supermoun62/Github_Projet_Train_Sons/Materiel_Projet_Trains_Sons/Materiels_Projet_Trains_Sons.pdf

Matériels_Projet_Train_Sons

# | Reference | Qty | Value | Footprint | TME-EU | TME-EU

1 | A1 | 1 | Arduino_Nano_v3.x | Module:Arduino_Nano
| Support mâle-femelle 15br | 2
2 | C1 | 1 | 330nf-25v | MesEmpreintes:CK06BX334K | CK06BX334K | ECQE2334KF
3 | C2 | 1 | 100nf-25v | MesEmpreintes:C_Disc_D5.0mm_W2.5mm_P2.50mm | CCK-100N
4 | C3 | 1 | 2200uf-35v | Capacitor_THT:CP_Radial_D17.0mm_P7.50mm | EEUFR1V222
5 | C4 | 1 | 47uf-16v | Capacitor_THT:CP_Radial_D5.0mm_P2.50mm | ECEA1CKS470
6 | D1 | 1 | B40C1500G | MesEmpreintes:B40C1500GE4851 | B40C1500G-E4/51
7 | D2 | 1 | 1N4007 | Diode_THT:D_DO-41_SOD81_P10.16mm_Horizontal | 1N4007-DC
8 | D3 | 1 | LED-5mm | LED_THT:LED_D5.0mm
9 | D4 | 1 | Busy | LED_THT:LED_D5.0mm
10 | D5 | 1 | Def SD | LED_THT:LED_D5.0mm
11 | D6 | 1 | E1 | LED_THT:LED_D5.0mm
12 | D7 | 1 | E2 | LED_THT:LED_D5.0mm
13 | F1 | 1 | | MesEmpreintes:Fuseholder_Cylinder-5x20mm_ Schurter_ZHL7X-H_Horizontal_Open | ZHL75
| F1 | 1 | | Support | ZHL7X-H
| Fusible | 1 | 250ma | | 0034.1510
14 | J1 | 1 | 1888690 | MesEmpreintes:MKDSN2,5-3-5,08-1888690 | MKDSN2.5/3-5.08
15 | J2, J3, J5, J8 | 4 | Conn_01x02_Socket | Connector_PinHeader_2.54mm:PinHeader_1x02_P2.54mm_Vertical
16 | J4 | 1 | Conn_01x05_Socket | Connector_PinHeader_2.54mm:PinHeader_1x05_P2.54mm_Vertical
17 | J6 | 1 | Conn_01x07_Socket | Connector_PinHeader_2.54mm:PinHeader_1x07_P2.54mm_Vertical
18 | J7 | 1 | Conn_01x03_Socket | Connector_PinHeader_2.54mm:PinHeader_1x03_P2.54mm_Vertical
19 | R1 | 1 | 1k-1 % | Resistor_THT:R_Axial_DIN0207_L6.3mm_D2.5mm_P2.54mm_Vertical | MBB02070C1001FCT00
20 | R2 | 1 | 4.7k-1% | Resistor_THT:R_Axial_DIN0207_L6.3mm_D2.5mm_P2.54mm_Vertical | MBA02040C4701FCT00
21 | R3, R8 | 2 | ? | Resistor_THT:R_Axial_DIN0207_L6.3mm_D2.5mm_P2.54mm_Vertical
22 | R4, R5, R6, R7, R9, R10 | 6 | 4.7K-1% | Resistor_THT:R_Axial_DIN0207_L6.3mm_D2.5mm_P2.54mm_Vertical | MBB02070C4701FCT00
23 | R11, R13, R14, R16 | 4 | 1k-1% | Resistor_THT:R_Axial_DIN0207_L6.3mm_D2.5mm_P2.54mm_Vertical | MBB02070C1001FCT00
24 | R12 | 1 | 1K-1% | Resistor_THT:R_Axial_DIN0207_L6.3mm_D2.5mm_P2.54mm_Vertical | MBB02070C1001FCT00
25 | R15 | 1 | 10K-1% | Resistor_THT:R_Axial_DIN0207_L6.3mm_D2.5mm_P2.54mm_Vertical | MBA02040C1002FCT00
26 | U1 | 1 | NTE1910_TO220 | MesEmpreintes:TO220_Horizontal_FK210SACB | NTE1910
| Refroidisseur | 1 | FK210SACB | | FK210SACB
27 | U2, U3 | 2 | 4N35 | Package_DIP:DIP-6_W7.62mm | 4N35-VIS
| Support | 2 | | | ICVT-6P
28 | U4 | 1 | TF-16P-V3.0 | MesEmpreintes:TF-16P-V3.0
| Support mâle-femelle 16br | 2
