supermoun62/Github_Projet_Train_Sons/Kicad_PDF_Projet_Train_Sons_V3/Kicad_Projet_Trains_Sons-F_Cu.pdf

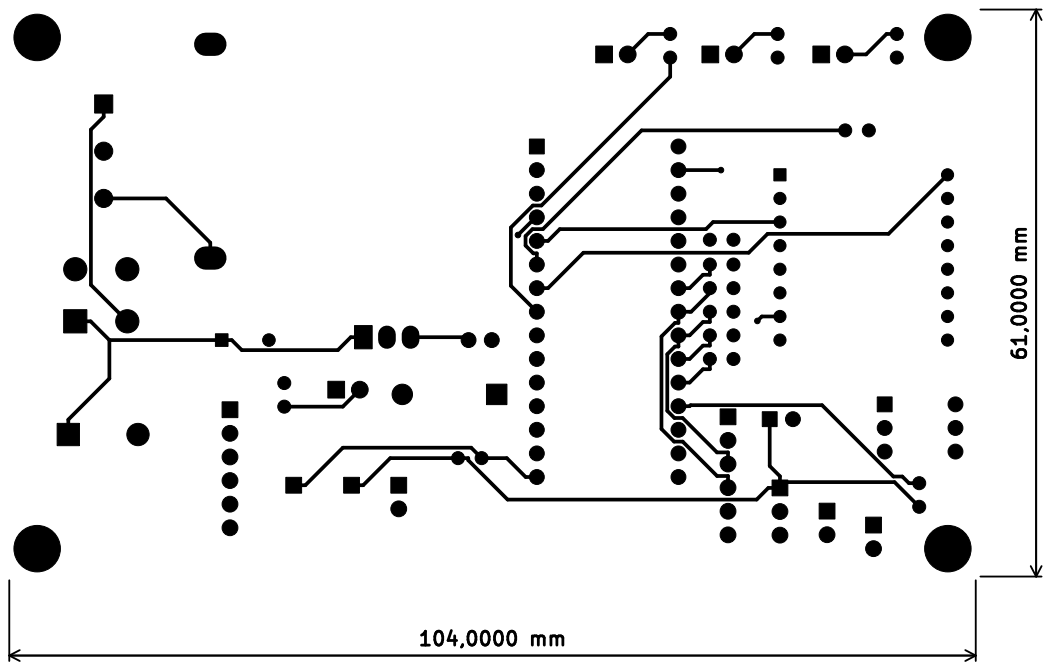
[picture p25: page 1]
