supermoun62/Github_Projet_Train_Sons/Kicad_PDF_Projet_Train_Sons_V3/Kicad_Projet_Trains_Sons-F_Fab.pdf

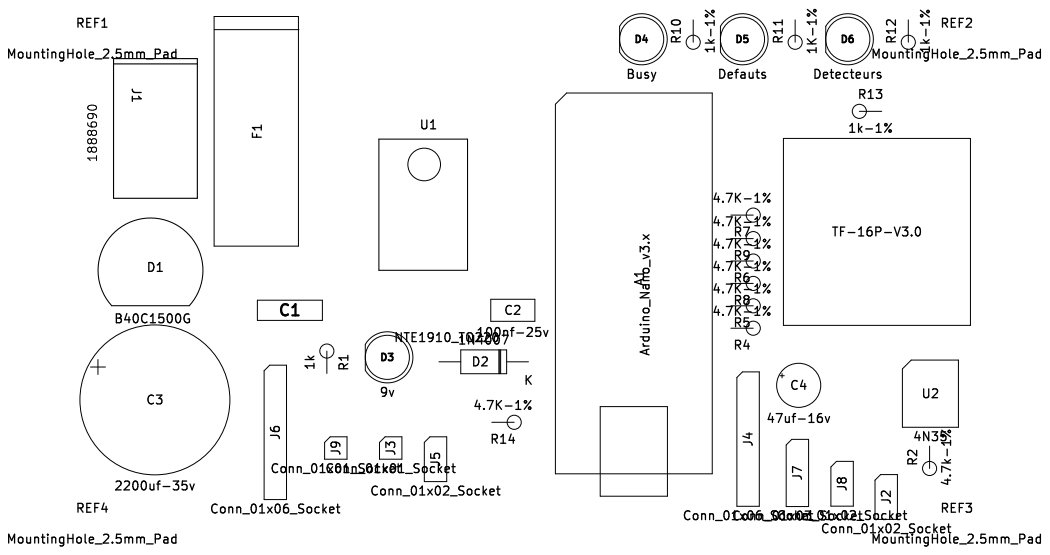
[picture p26: page 1]
