supermoun62/Github_Projet_Train_Sons/Kicad_PDF_Projet_Train_Sons_V3/Kicad_Projet_Trains_Sons-F_Silkscreen.pdf

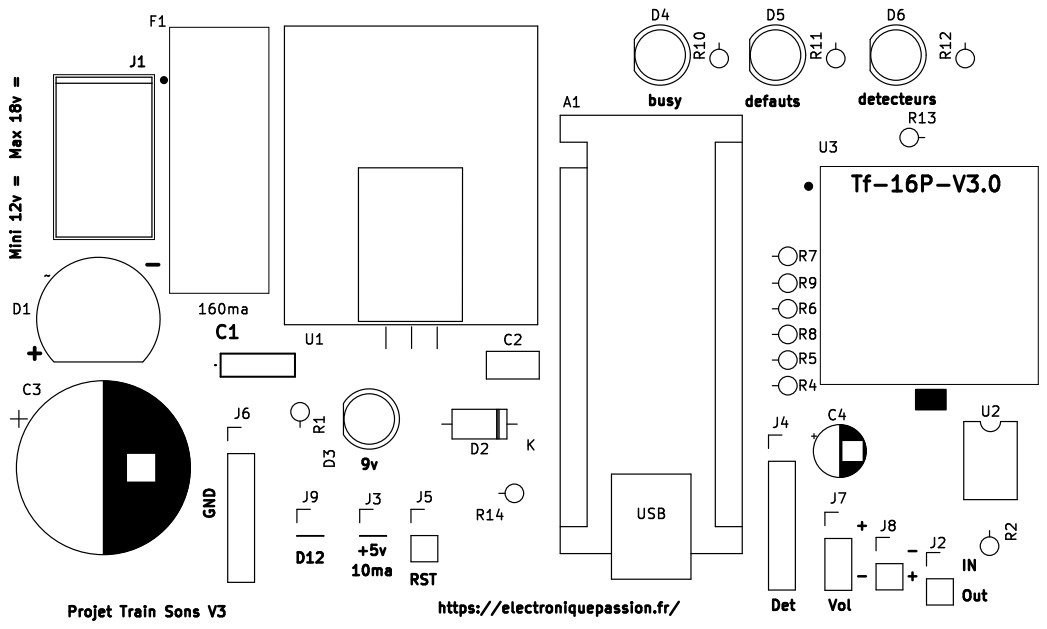
[picture p27: page 1]
