supermoun62/Github_Projet_Train_Sons/Kicad_PDF_Projet_Train_Sons_V3/Kicad_Projet_Trains_Sons-User_Comments.pdf

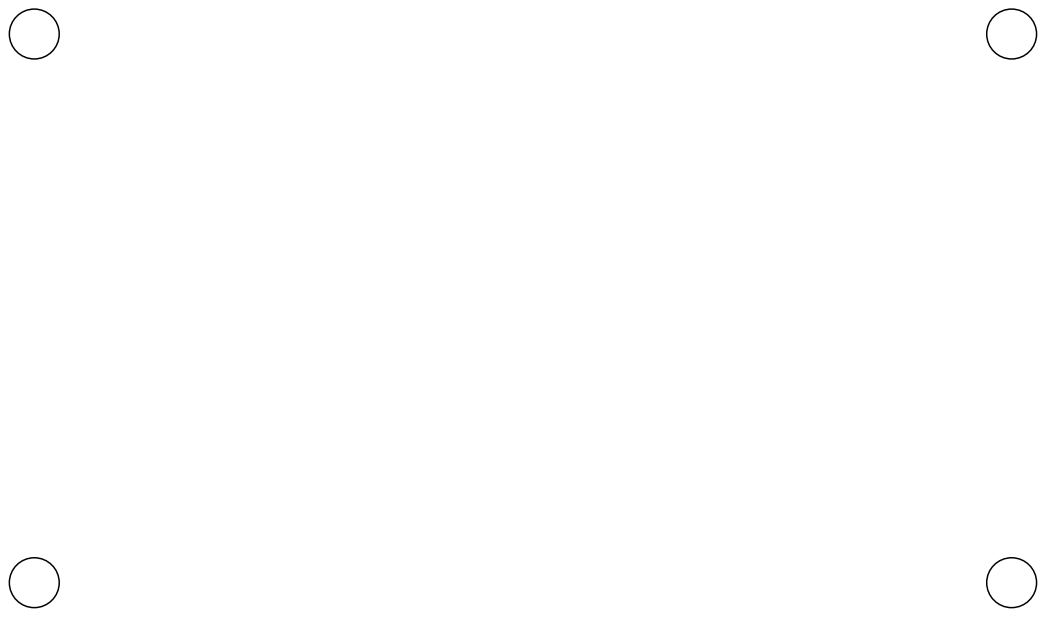
[picture p28: page 1]
