supermoun62/Github_Projet_Train_Sons/Arduino_Train_Son_DFPlayer_Prog_V5/Arduino_Train_Son_DFPlayer_Prog_V5.ino

/*
 Description: Programme V2 permettant la diffusion d'un son avec un DFPlayerMini 
  Carte   : Arduino Nano
  DFPlayerMini (Mp3 TF 16P V3.0)

Librairies utilisées:DFRobotDFPlayerMini.h 
                        https://github.com/DFRobot/DFRobotDFPlayerMini 
                        SoftwareSerial.h
                     
 Informations sites:    https://lasonotheque.org/dossier-62-fabriquer-boite-sons-arduino-dfplayer.html

                        https://docs.arduino.cc/learn/built-in-libraries/software-serial/

                        https://idehack.com/dfplayer-mp3-tf-16p-et-arduino/
                        
                        https://lasonotheque.org/fabriquer-boite-sons-arduino-dfplayer_f62.html

                        https://wiki.dfrobot.com/DFPlayer_Mini_SKU_DFR0299#Connection_Diagram

                        https://wiki.dfrobot.com/DFPlayer_Mini_SKU_DFR0299

                        https://www.wikidebrouillard.org/wiki/Item:DFPlayer_Lecteur_MP3 
  
  Auteur:  Christian Mercier  
  Créé le: 03/03/2024 
  62128 Boiry-Becquerelle France                                        
*/
#include "SoftwareSerial.h"
#include "DFRobotDFPlayerMini.h"
//--------------------------------------------
const byte RXPIN = 2;
const byte TXPIN = 3;
SoftwareSerial mySerial(RXPIN, TXPIN);
DFRobotDFPlayerMini myDFPlayer;
//--------------------------------------------
const int DET0 = A0;
const int DET1 = A1;
const int DET2 = A2;
const int DET3 = A3;
//             = A4;// SDA
//             = A5;// SCL
const int DET6 = A6;
const int potarVolume = A7;

int etatDet0 = 1023;
int etatDet1 = 1023;
int etatDet2 = 1023;
int etatDet3 = 1023;
int etatDET6 = 1023;
int etatPotarVolume = 1023;
int valVolume = 0;
const byte PINBUSY = 4;
const byte LEDBUSY = 5;
const byte LEDDEFAUT = 6;

int valUpSon = 0;
byte etatPinBusy= 0;
void setup()
{
  mySerial.begin(9600);
  Serial.begin(9600);
//-------------------------------------------- 
if (!myDFPlayer.begin(mySerial))
  {
    Serial.println(F("Pb communication : verifier SDcard"));
    digitalWrite(LEDDEFAUT, HIGH);
    while(true);
  }
//--------------------------------------------  
  myDFPlayer.setTimeOut(500);  
  myDFPlayer.volume(5);
  //myDFPlayer.play(1);
//--------------------------------------------
  pinMode(DET0, INPUT);
  pinMode(DET1, INPUT);
  //pinMode(DET2, INPUT);
  //pinMode(Det3, INPUT);
  pinMode(DET6, INPUT);
  pinMode(potarVolume, INPUT);
  pinMode(PINBUSY, INPUT);
  pinMode(LEDBUSY, OUTPUT);
  pinMode(PINBUSY, INPUT);
  pinMode(LEDDEFAUT, OUTPUT);
  delay(5000);
}//Fin SETUP

void loop()
{
  etatDet0 = analogRead(DET0);
  etatDet1 = analogRead(DET1);
  etatDET6 = analogRead(DET6);
  etatPotarVolume = analogRead(potarVolume);
  etatPinBusy = digitalRead(PINBUSY);
//--------------------------------------------
  if(etatDet0 <= 512 && etatPinBusy == 1)
    {
      myDFPlayer.play(1);      
    }
//-------------------------------------------- 
  if(etatDet1 <= 512 && etatPinBusy == 1)
    {
      myDFPlayer.play(2);      
    }
//--------------------------------------------
valVolume = map(analogRead(A7),0,1023,0,30);
myDFPlayer.volume(valVolume);
//--------------------------------------------
  if(etatPinBusy == 0)// Niveau bas en lecture, niveau haut en veille
    {
      digitalWrite(LEDBUSY,HIGH);
    }
  else
    {
      digitalWrite(LEDBUSY,LOW);
    }
//--------------------------------------------
Serial.print(etatDet0);
Serial.print("\t");
Serial.print(etatDet1);
Serial.print("\t");
Serial.print(etatDet2);
Serial.print("\t");
Serial.print(etatDet3);
Serial.print("\t");
Serial.print(etatDET6);
Serial.print("\t");
Serial.print("\t");
Serial.print(etatPotarVolume);
Serial.print("\t");
Serial.print(valVolume); 
Serial.print("\t");
Serial.print(myDFPlayer.readVolume());//  Renvoi le volume du DFPlayer
Serial.print("\t");
Serial.print("\t");
Serial.print(etatPinBusy);
Serial.println("\t");

}//FIN LOOP
